electricui/electricui-arena/hardware/output/board-bottom.png

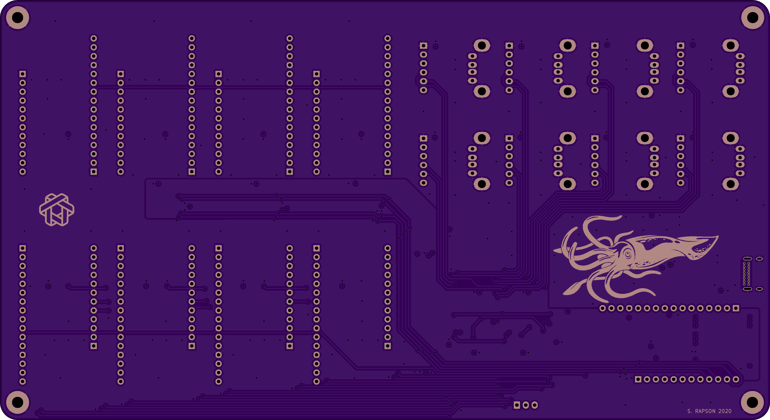
hardware/output/board-bottom.png
