electricui/electricui-arena/hardware/output/board-top.png

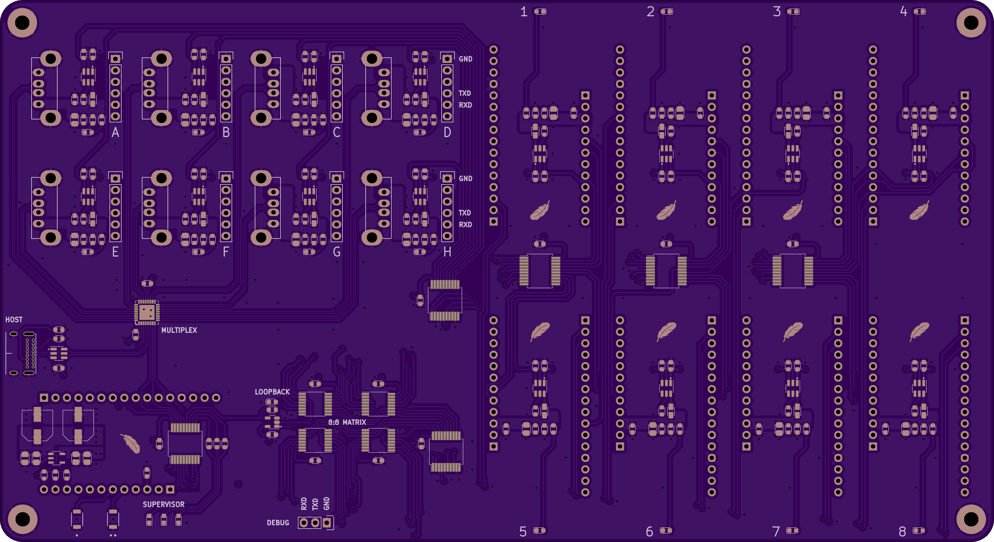
hardware/output/board-top.png
