electricui/electricui-arena/firmware/hardware_test/networking.h

/* -------------------------------------------------------------------------- */

void setup_ethernet( void );

/* -------------------------------------------------------------------------- */

void handle_ethernet( void );

/* -------------------------------------------------------------------------- */
